matiasmicheletto/lidar-scanner/Data/charts/AnalisisViento.png

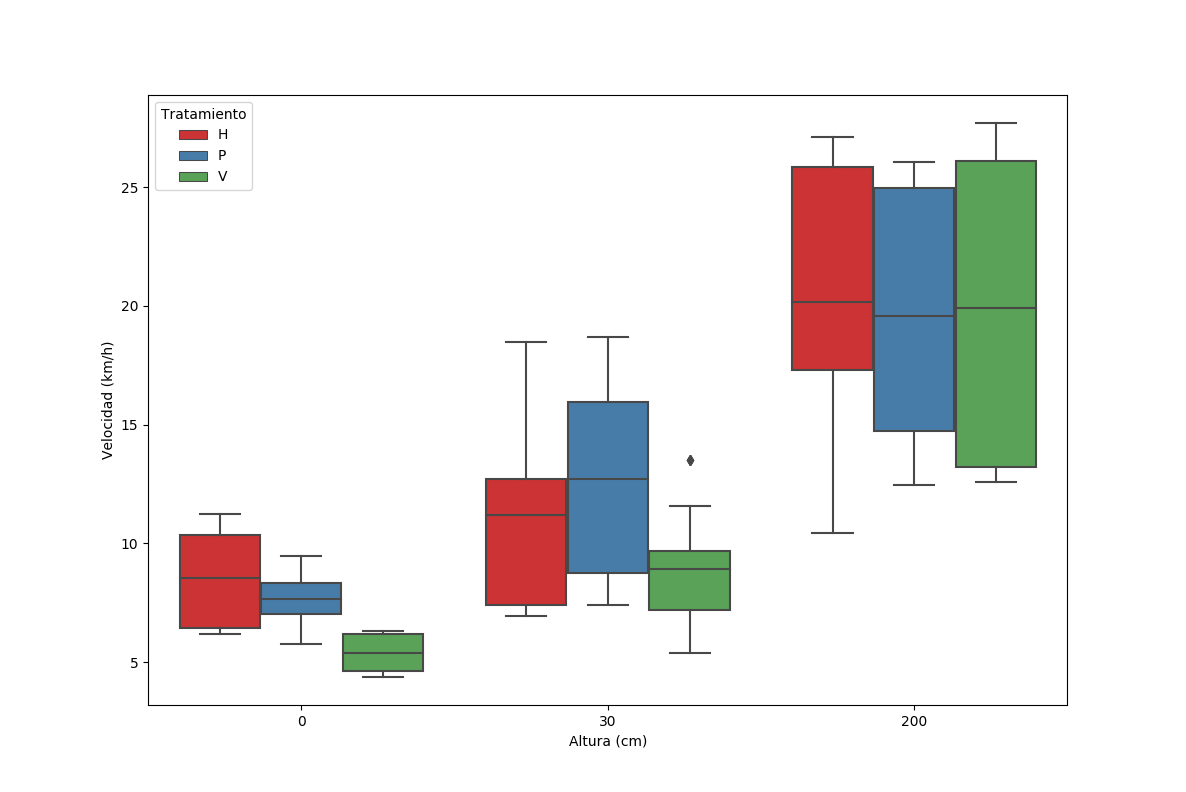
Data/charts/AnalisisViento.png
