matiasmicheletto/lidar-scanner/Data/charts/Clasif.png

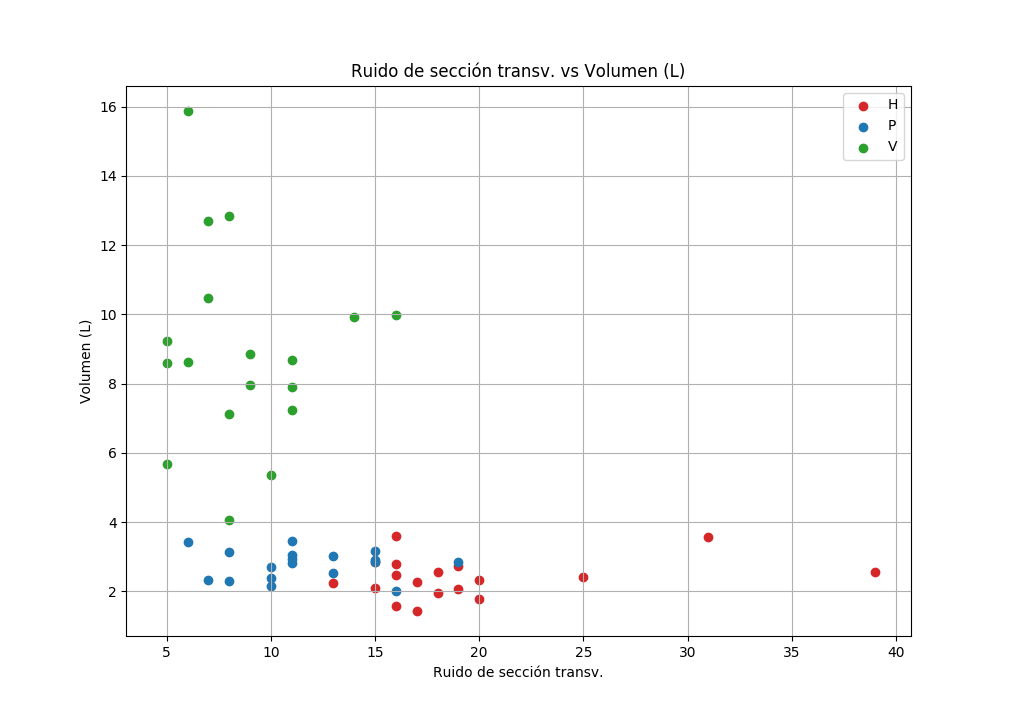
Data/charts/Clasif.png
