matiasmicheletto/lidar-scanner/Data/charts/Comparat.png

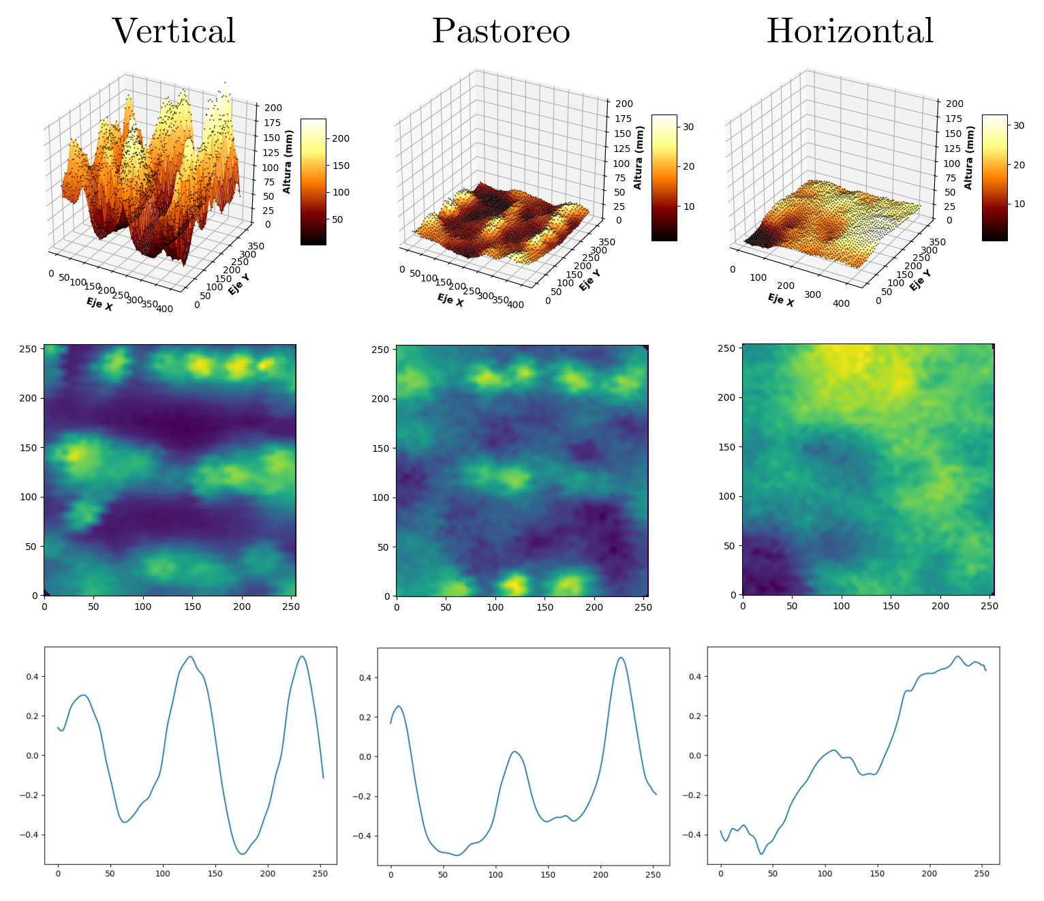
Data/charts/Comparat.png
