matiasmicheletto/lidar-scanner/Data/charts/compare/19_2_21_B3P3GS.png

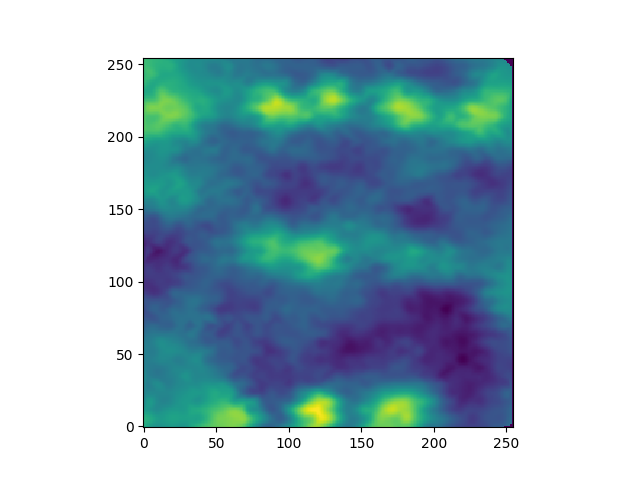
Data/charts/compare/19_2_21_B3P3GS.png
