matiasmicheletto/lidar-scanner/Data/charts/compare/19_2_21_B3P33D.png

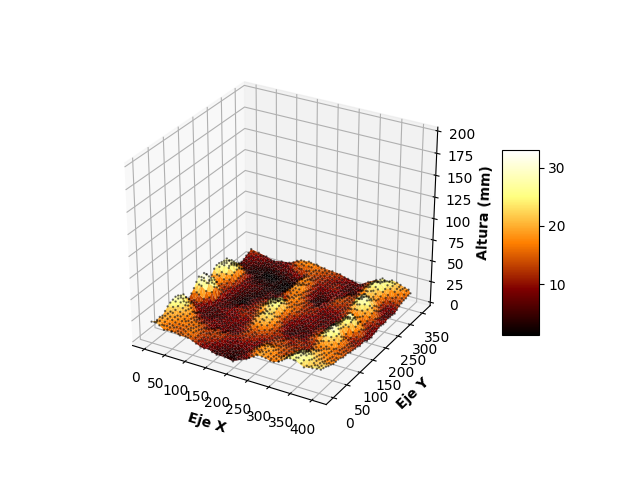
Data/charts/compare/19_2_21_B3P33D.png
