matiasmicheletto/lidar-scanner/Data/charts/compare/19_2_21_B3V2XS.png

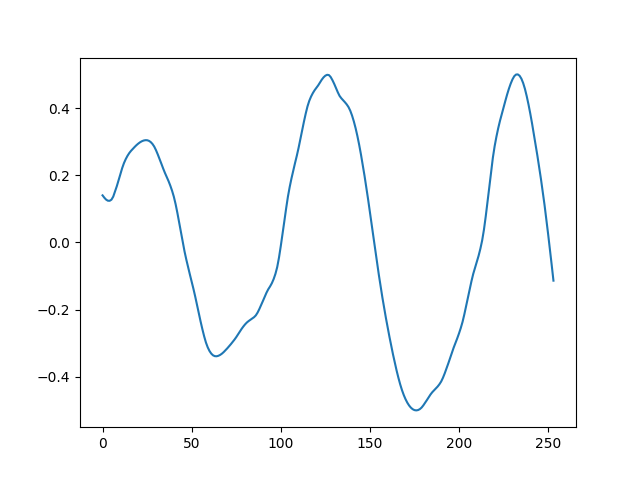
Data/charts/compare/19_2_21_B3V2XS.png
