matiasmicheletto/lidar-scanner/Data/charts/compare/20_5_26_B1H2GS.png

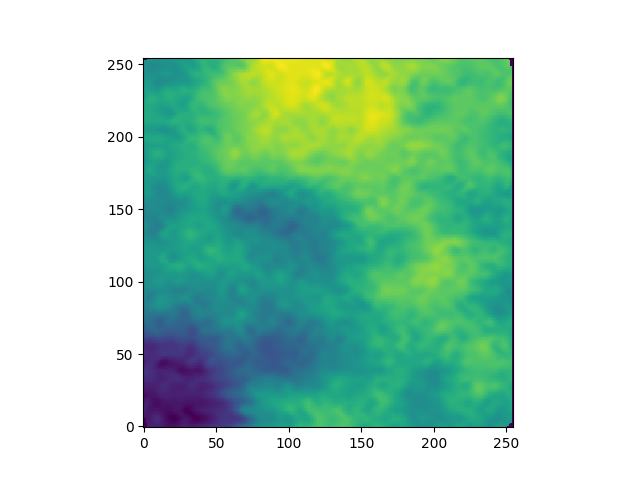
Data/charts/compare/20_5_26_B1H2GS.png
