matiasmicheletto/lidar-scanner/Data/charts/compare/20_5_26_B1H23D.png

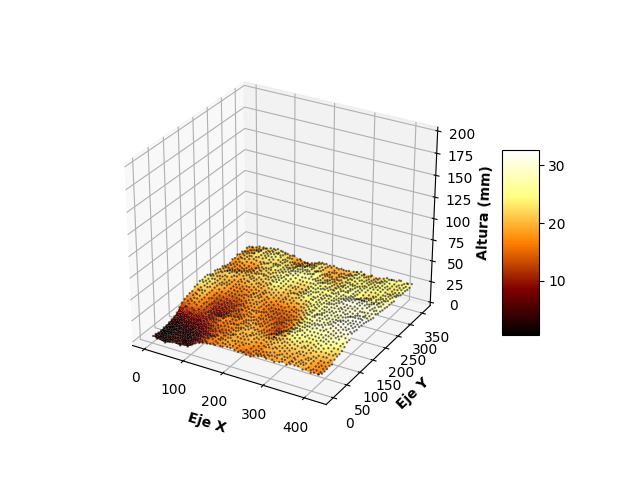
Data/charts/compare/20_5_26_B1H23D.png
