matiasmicheletto/lidar-scanner/Data/charts/ConfusionMatrix.png

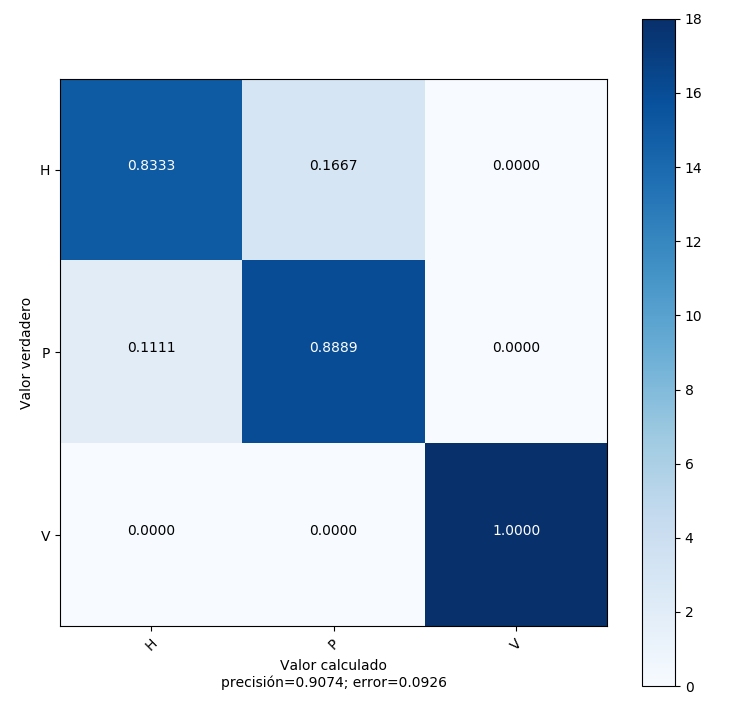
Data/charts/ConfusionMatrix.png
