matiasmicheletto/lidar-scanner/Data/charts/LDA.png

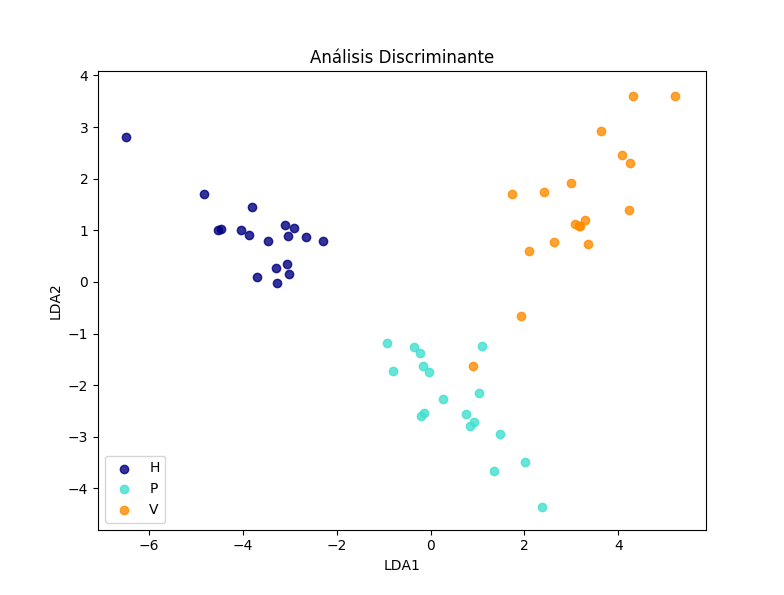
Data/charts/LDA.png
