matiasmicheletto/lidar-scanner/Data/charts/Temps.png

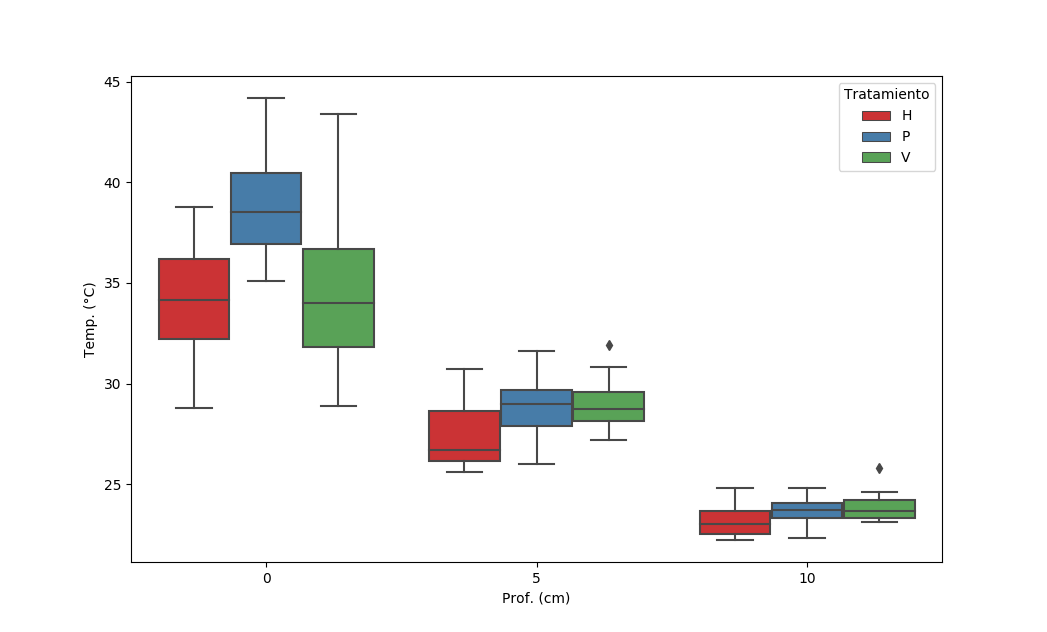
Data/charts/Temps.png
