matiasmicheletto/lidar-scanner/Data/charts/vol_vs_ms.png

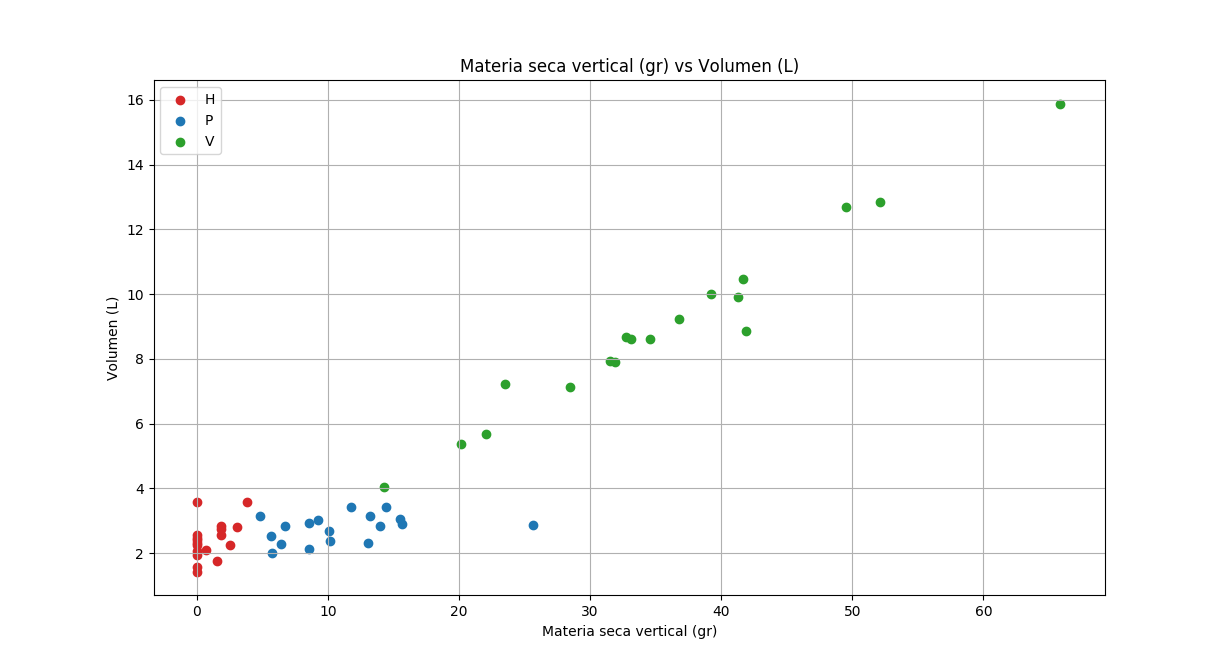
Data/charts/vol_vs_ms.png
