matiasmicheletto/lidar-scanner/Data/xsection/19_2_21_B1P1.png

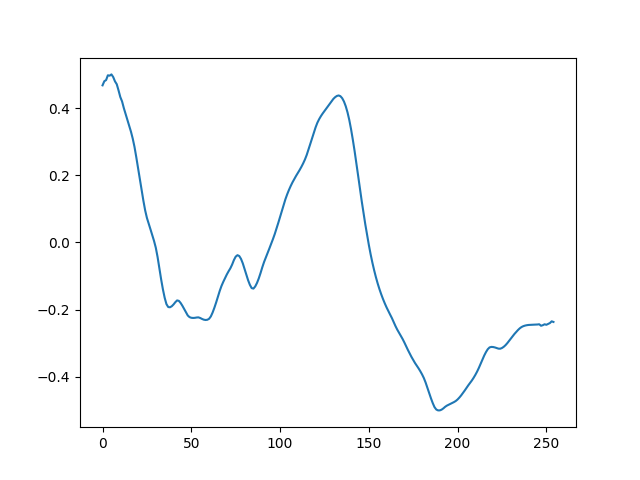
Data/xsection/19_2_21_B1P1.png
