matiasmicheletto/lidar-scanner/Data/xsection/19_2_21_B1V3.png

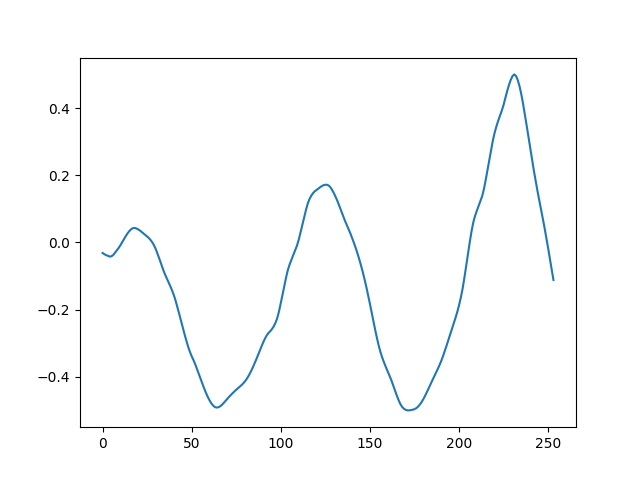
Data/xsection/19_2_21_B1V3.png
