matiasmicheletto/lidar-scanner/Data/xsection/19_2_21_B2H1.png

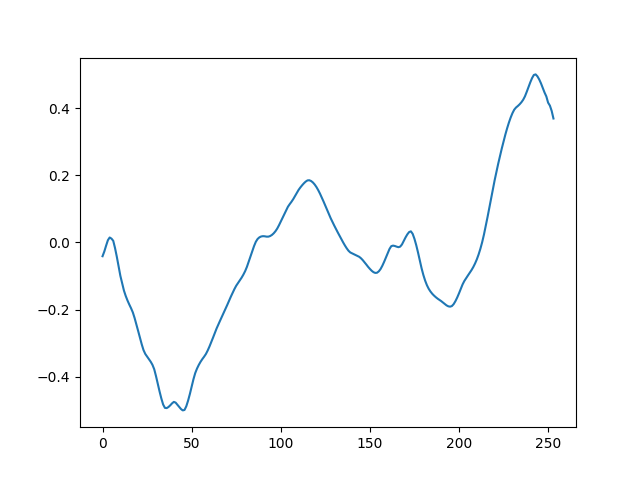
Data/xsection/19_2_21_B2H1.png
