matiasmicheletto/lidar-scanner/Data/xsection/19_2_21_B2P3.png

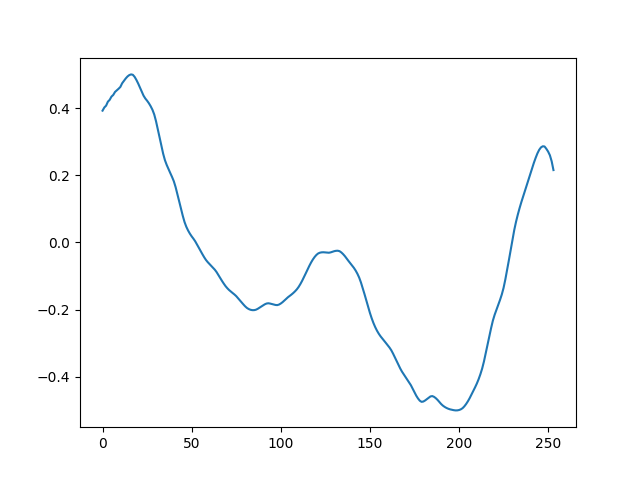
Data/xsection/19_2_21_B2P3.png
