matiasmicheletto/lidar-scanner/Data/xsection/19_2_21_B3H2.png

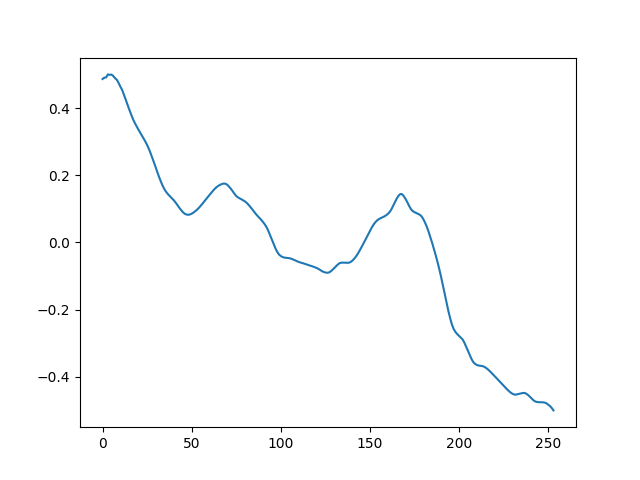
Data/xsection/19_2_21_B3H2.png
