matiasmicheletto/lidar-scanner/Data/xsection/20_5_26_B1H1.png

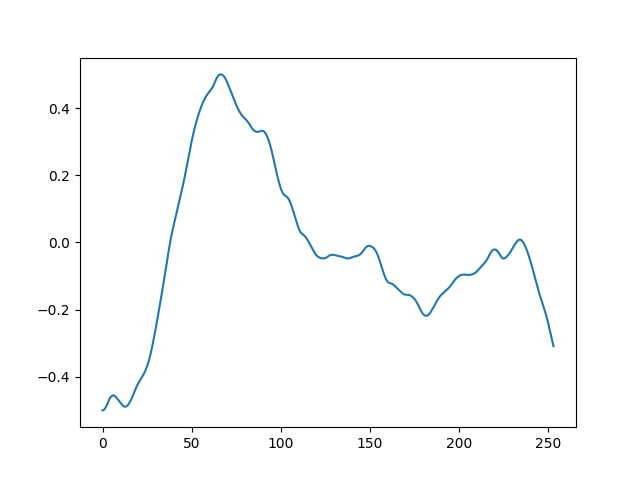
Data/xsection/20_5_26_B1H1.png
