matiasmicheletto/lidar-scanner/Data/xsection/20_5_26_B1H2.png

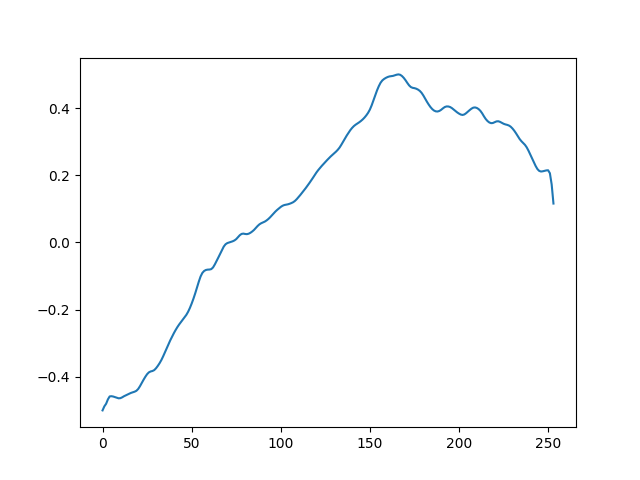
Data/xsection/20_5_26_B1H2.png
