matiasmicheletto/lidar-scanner/Data/xsection/20_5_26_B1P2.png

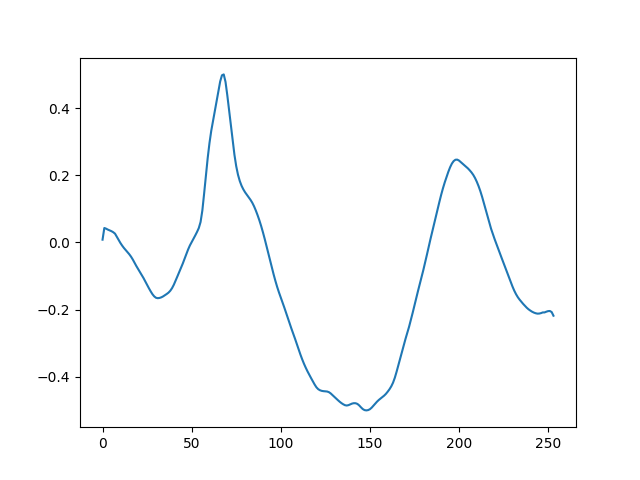
Data/xsection/20_5_26_B1P2.png
