matiasmicheletto/lidar-scanner/Data/xsection/20_5_26_B1V2.png

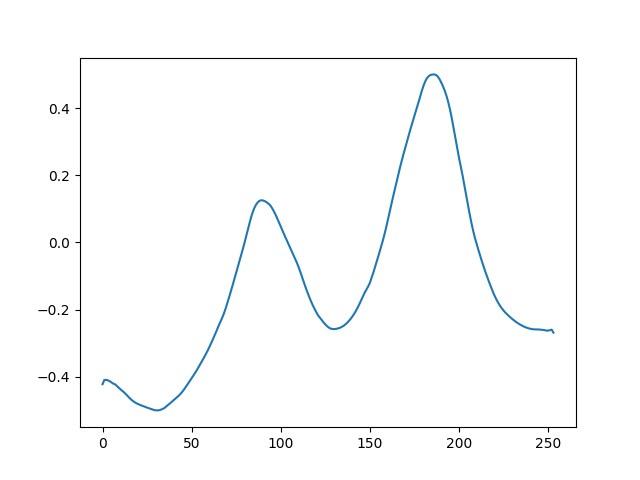
Data/xsection/20_5_26_B1V2.png
