matiasmicheletto/lidar-scanner/Data/xsection/20_5_26_B1V3.png

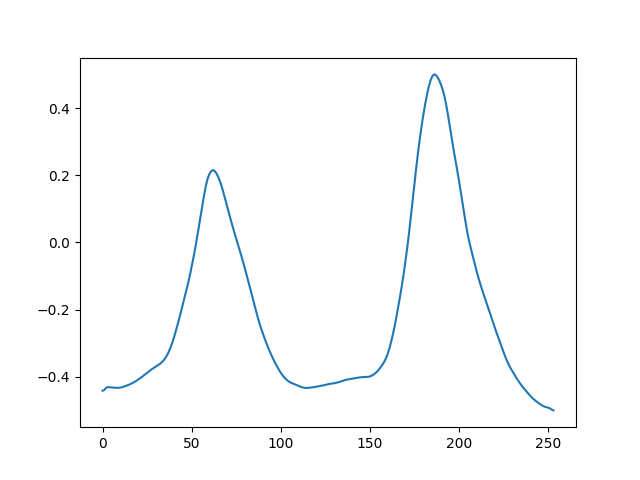
Data/xsection/20_5_26_B1V3.png
