matiasmicheletto/lidar-scanner/Data/xsection/20_5_26_B2H2.png

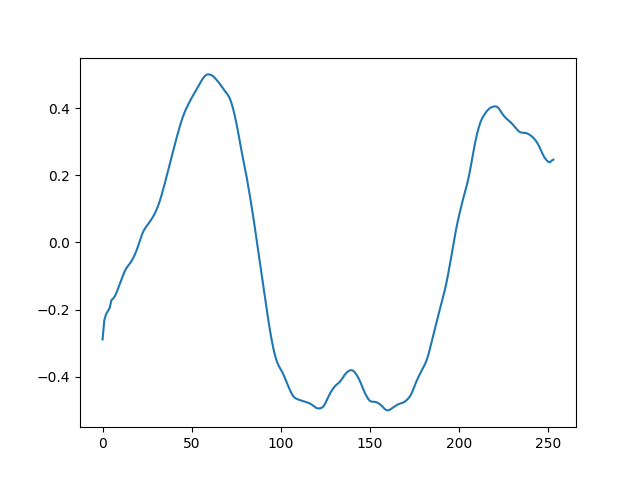
Data/xsection/20_5_26_B2H2.png
