matiasmicheletto/lidar-scanner/Data/xsection/20_5_26_B2P1.png

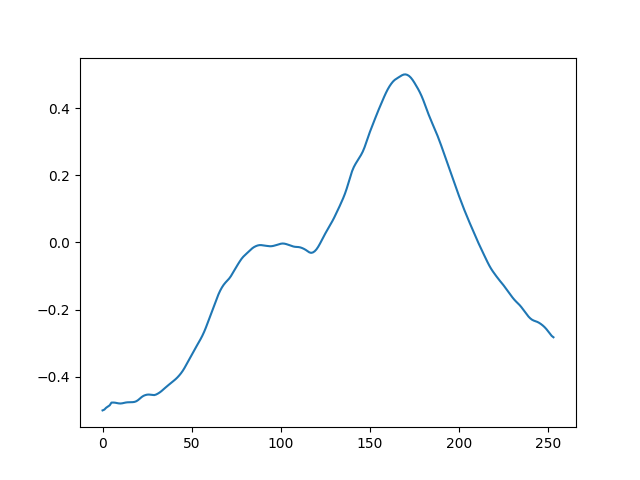
Data/xsection/20_5_26_B2P1.png
