matiasmicheletto/lidar-scanner/Data/xsection/20_5_26_B2P2.png

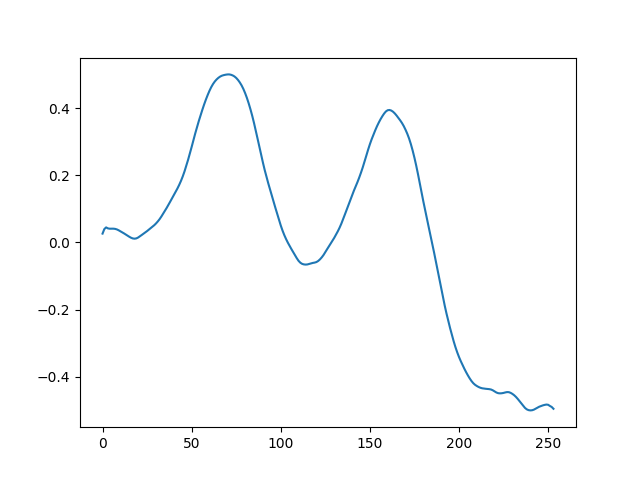
Data/xsection/20_5_26_B2P2.png
