matiasmicheletto/lidar-scanner/Data/xsection/20_5_26_B2P3.png

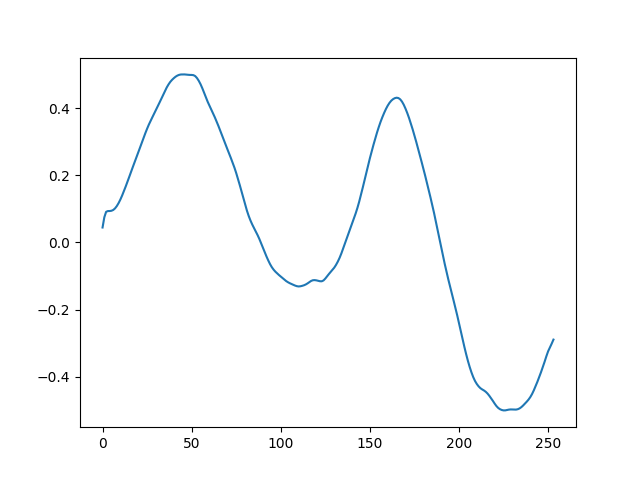
Data/xsection/20_5_26_B2P3.png
