matiasmicheletto/lidar-scanner/Data/xsection/20_5_26_B3P1.png

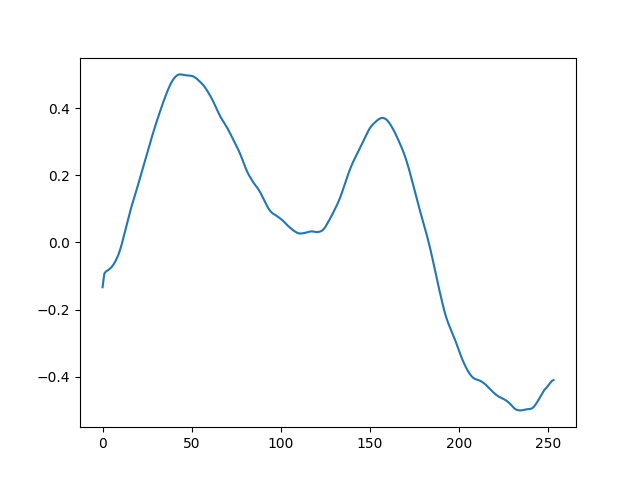
Data/xsection/20_5_26_B3P1.png
