matiasmicheletto/lidar-scanner/Data/xsection/20_5_26_B3V2.png

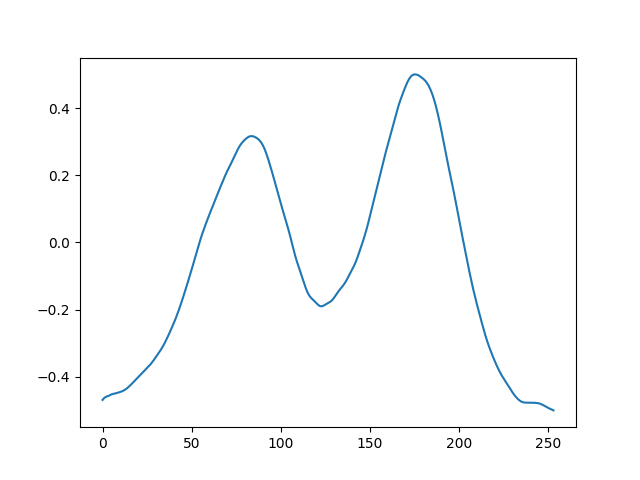
Data/xsection/20_5_26_B3V2.png
