matiasmicheletto/lidar-scanner/Datasheets/arduino_nano.png

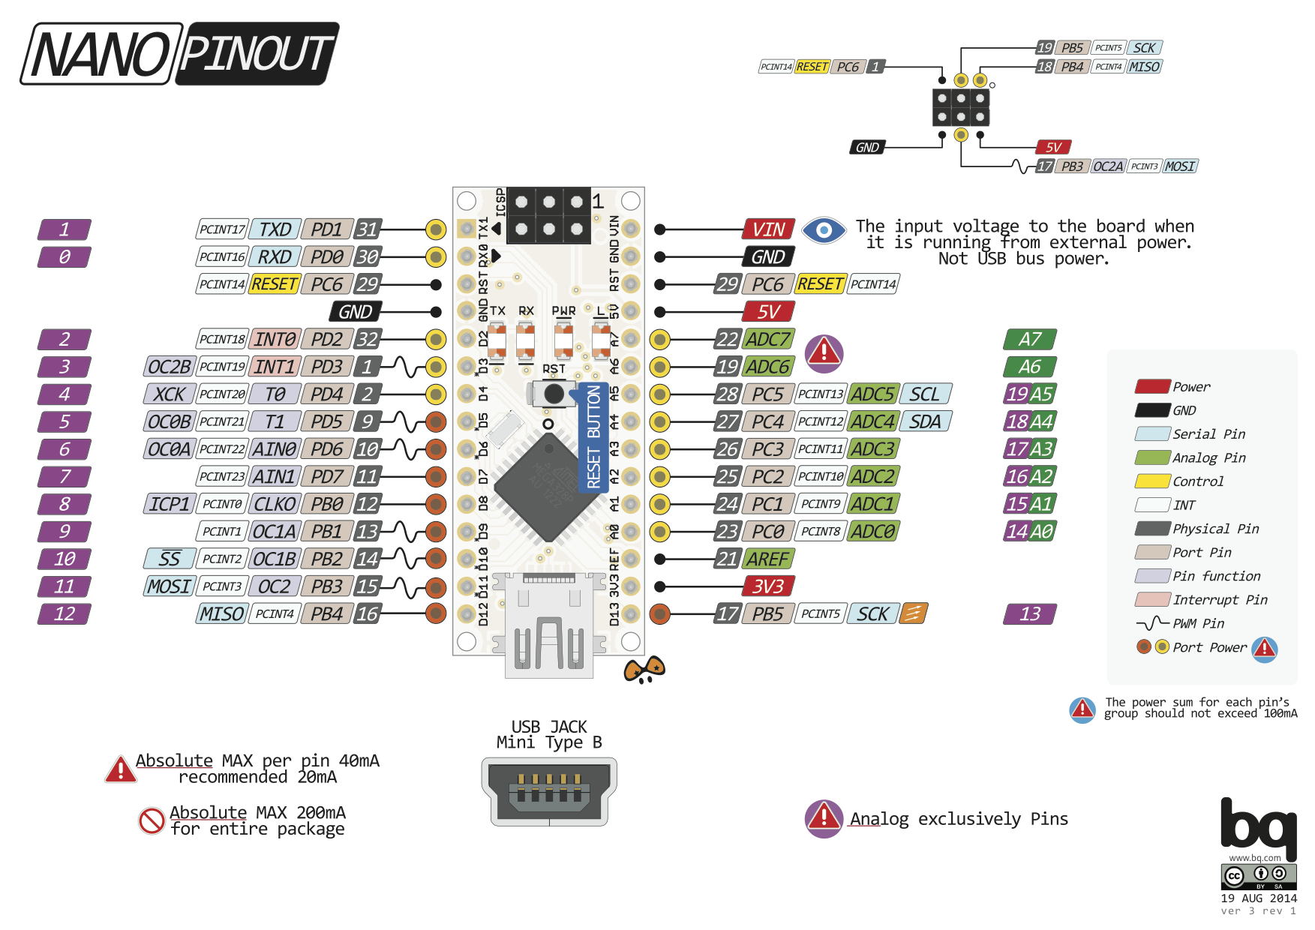
Datasheets/arduino_nano.png
