matiasmicheletto/lidar-scanner/Img/Campo2.jpeg

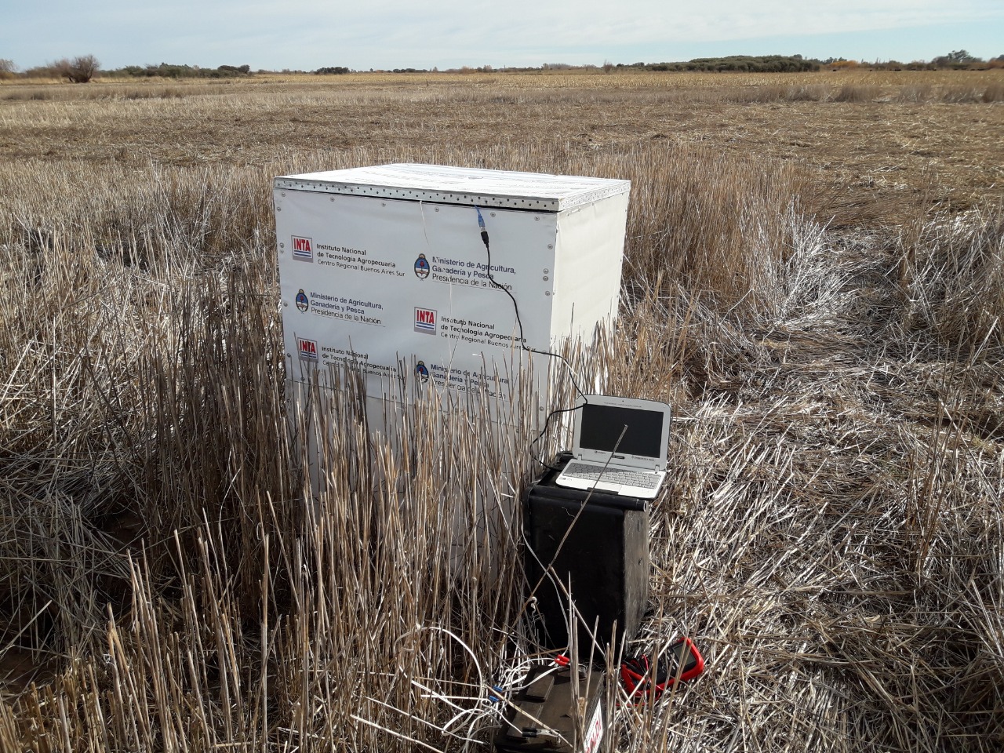
Img/Campo2.jpeg
