matiasmicheletto/lidar-scanner/Img/Estructura.jpeg

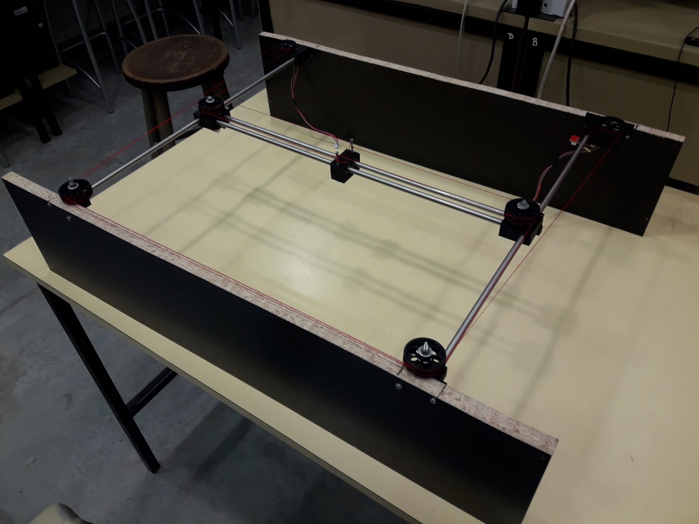
Img/Estructura.jpeg
