matiasmicheletto/lidar-scanner/Img/HRes.png

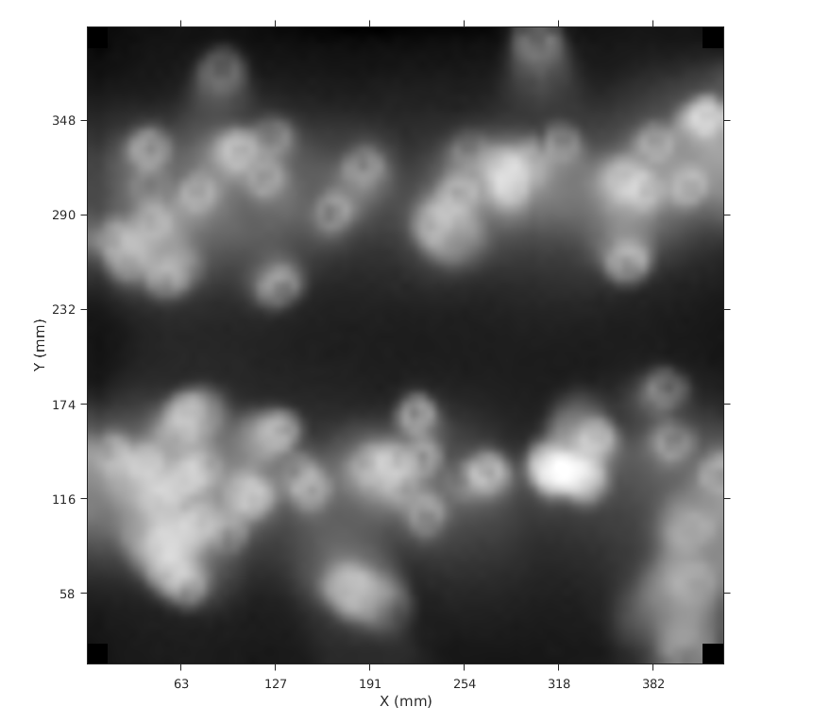
Img/HRes.png
