matiasmicheletto/lidar-scanner/Img/PCB.jpeg

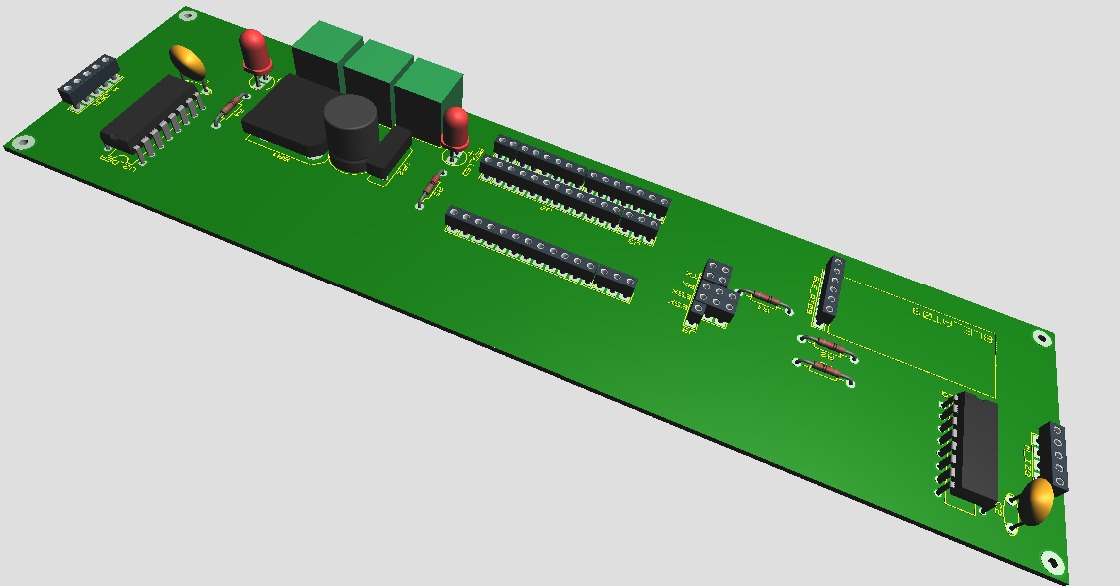
Img/PCB.jpeg
