matiasmicheletto/lidar-scanner/PCB/PCB_Scanner.BMP

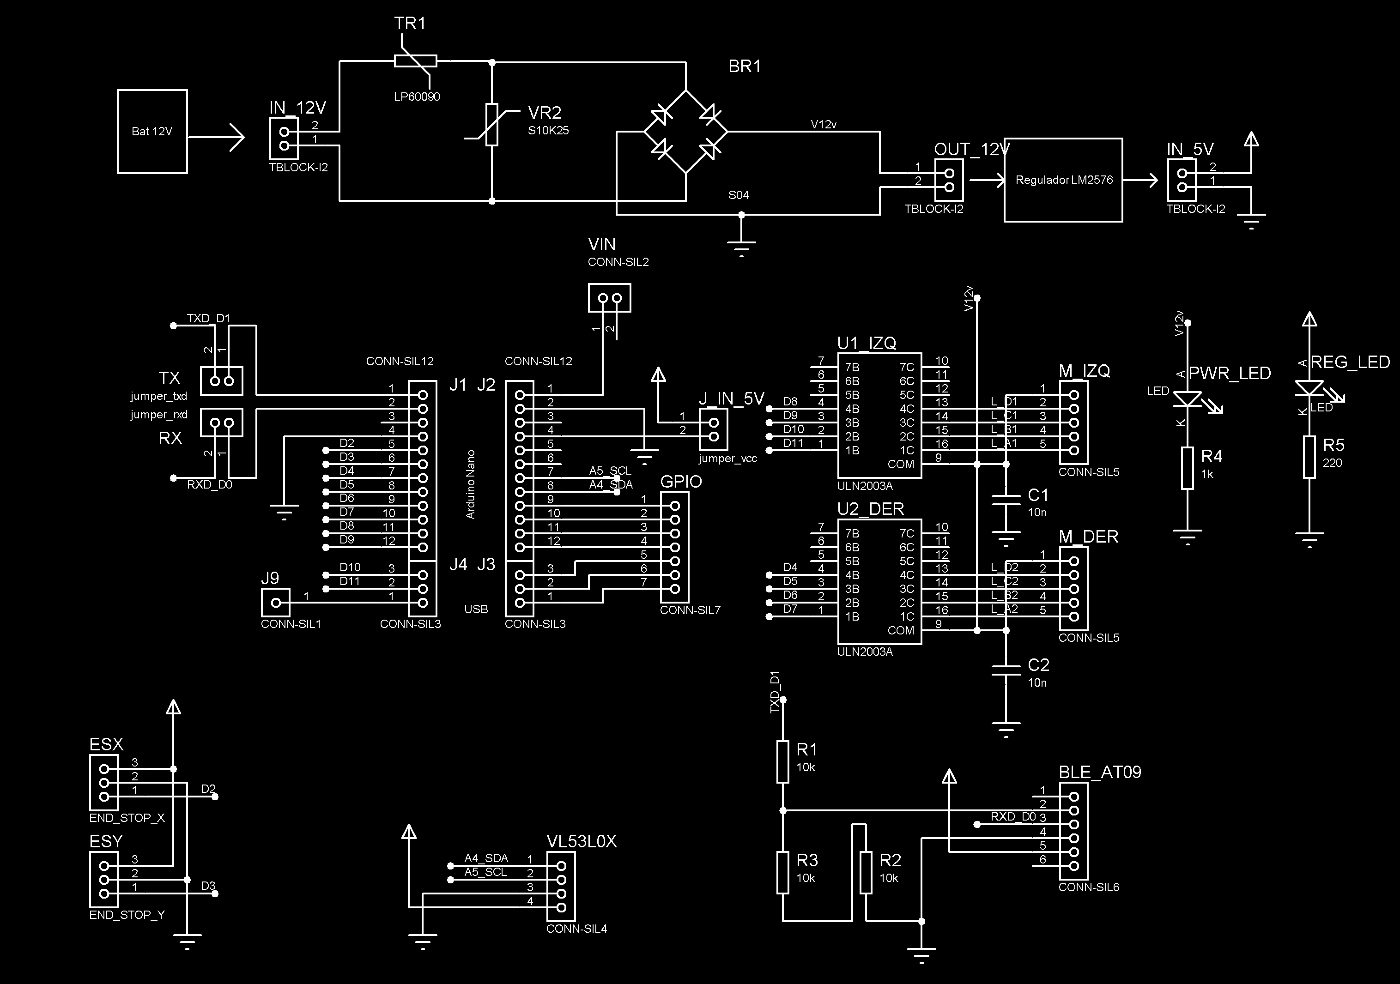
PCB/PCB_Scanner.BMP
