matiasmicheletto/lidar-scanner/Firmware/TestLaser/TestLaser.ino

#include <Wire.h>
#include "VL53L0X.h"

VL53L0X sensor;

void setup()
{
  Serial.begin(9600);
  Wire.begin();
  sensor.init();
  sensor.setTimeout(500);
  sensor.setMeasurementTimingBudget(200000); // Modo high accuracy
}

void loop()
{
  Serial.print(sensor.readRangeSingleMillimeters());
  if (sensor.timeoutOccurred()) { Serial.print(" TIMEOUT"); }
  Serial.println();
  delay(500);
}
